vives-project-xp/GreenhouseSecurity/images/affiche-canvas.png

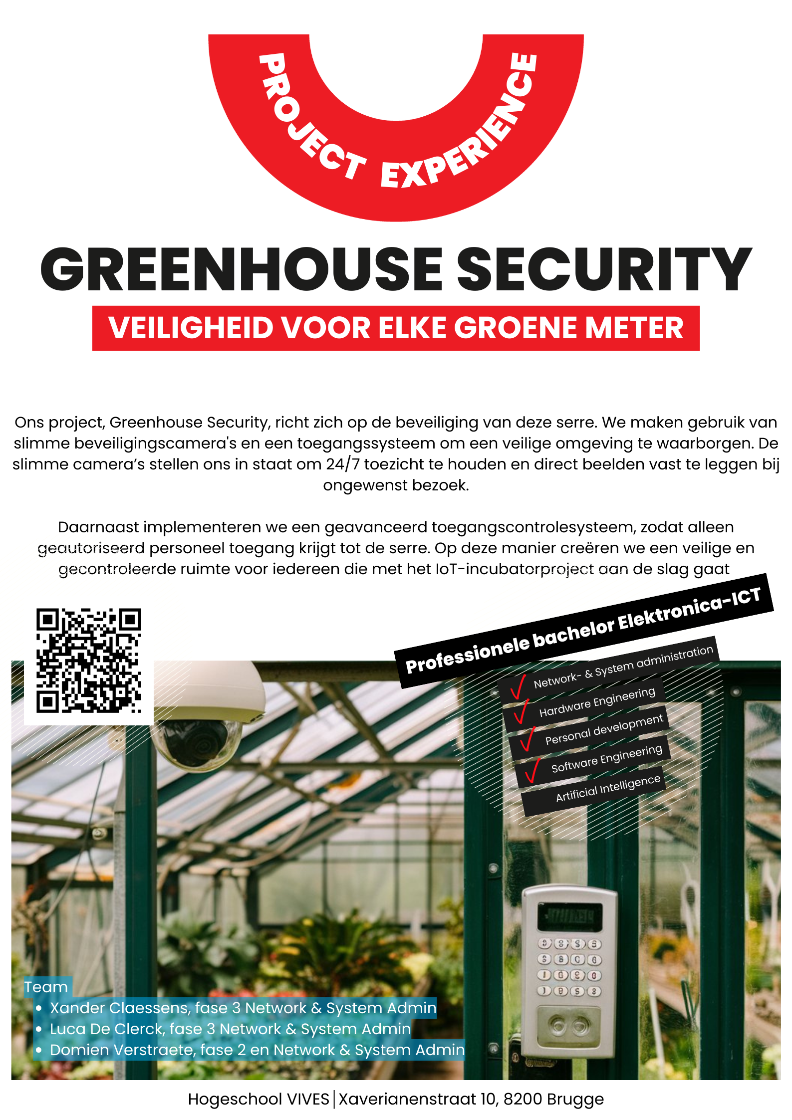
images/affiche-canvas.png
