vives-project-xp/GreenhouseSecurity/images/Architectuur.png

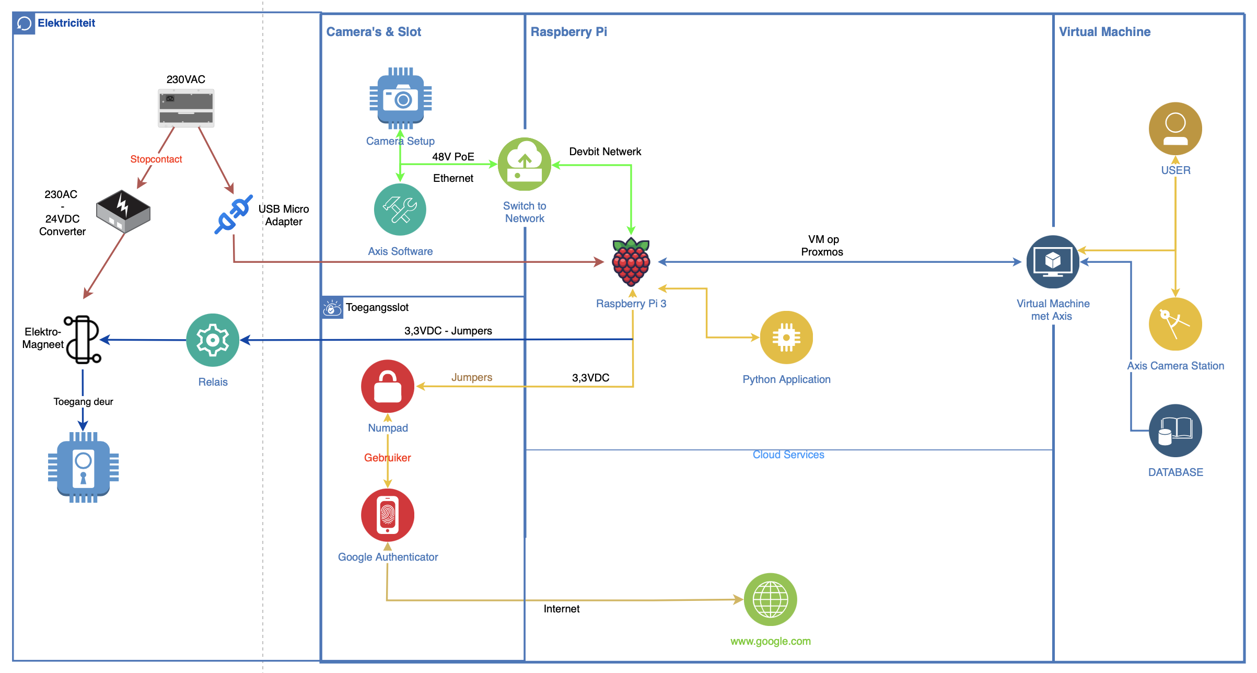
images/Architectuur.png
