vives-project-xp/GreenhouseSecurity/images/axis-application-views.png

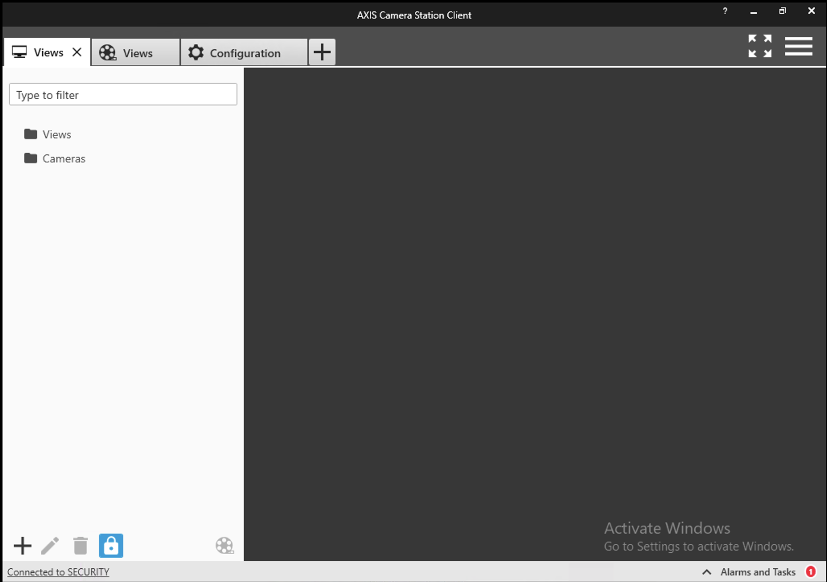
images/axis-application-views.png
