vives-project-xp/GreenhouseSecurity/images/axis.jpg

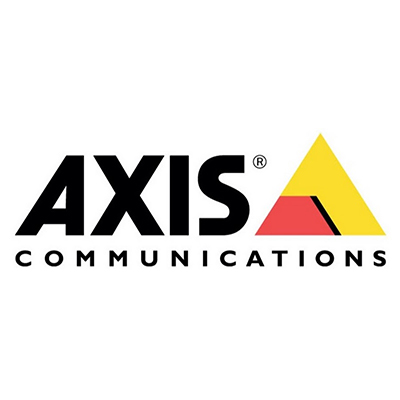
images/axis.jpg
