vives-project-xp/GreenhouseSecurity/images/BiometricImage04192022.jpg

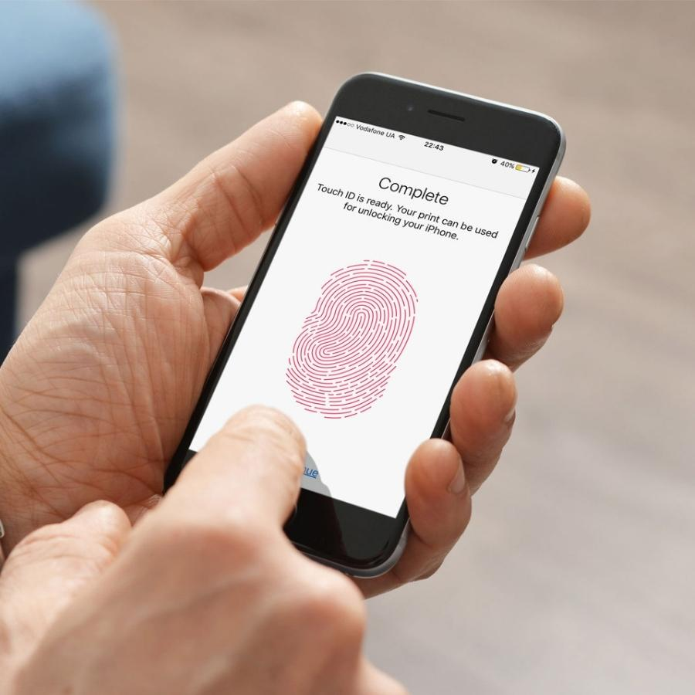
images/BiometricImage04192022.jpg
