vives-project-xp/GreenhouseSecurity/images/camera-dak.jpg

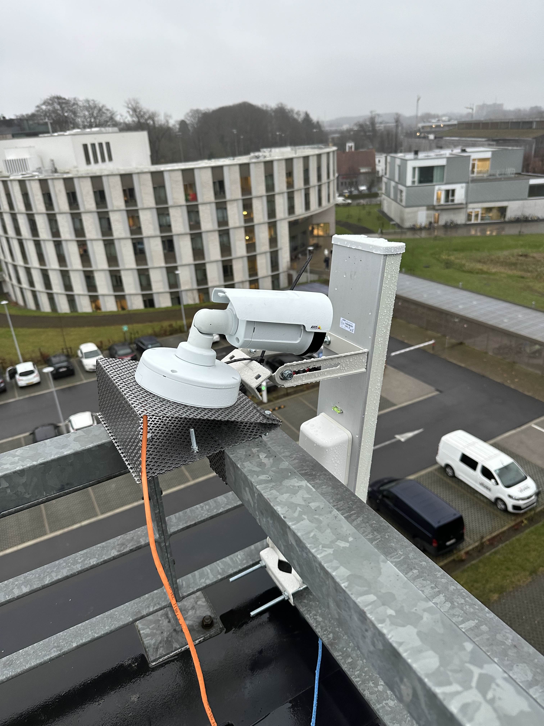
images/camera-dak.jpg
