vives-project-xp/GreenhouseSecurity/images/camera-in-serre.jpg

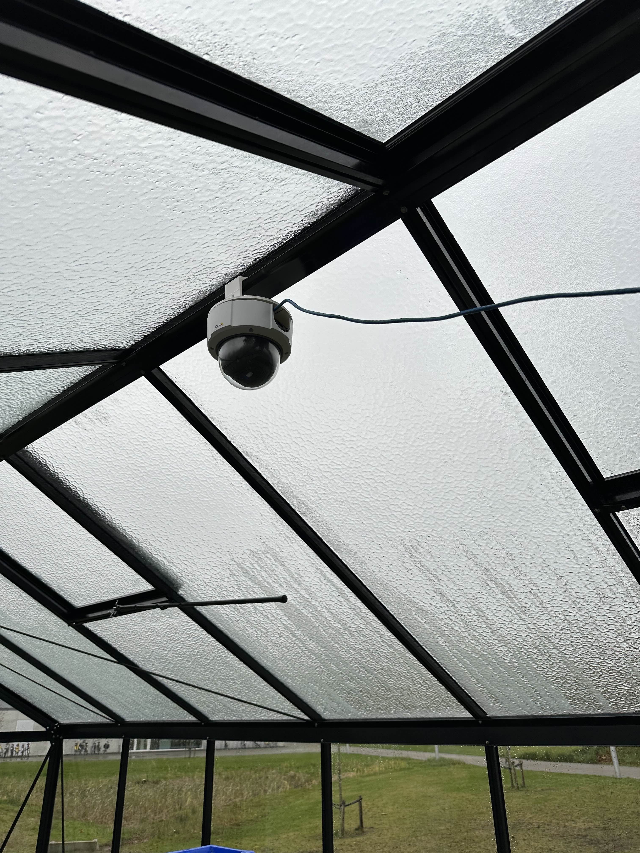
images/camera-in-serre.jpg
