vives-project-xp/GreenhouseSecurity/images/camera-view.png

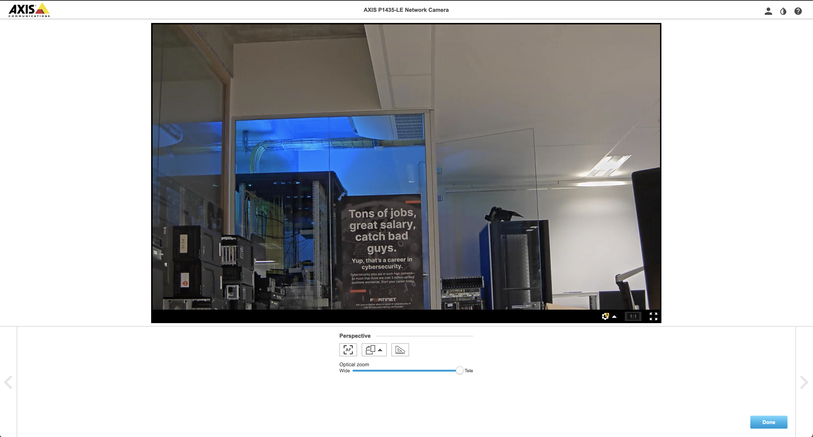
images/camera-view.png
