vives-project-xp/GreenhouseSecurity/images/domeCamera.webp

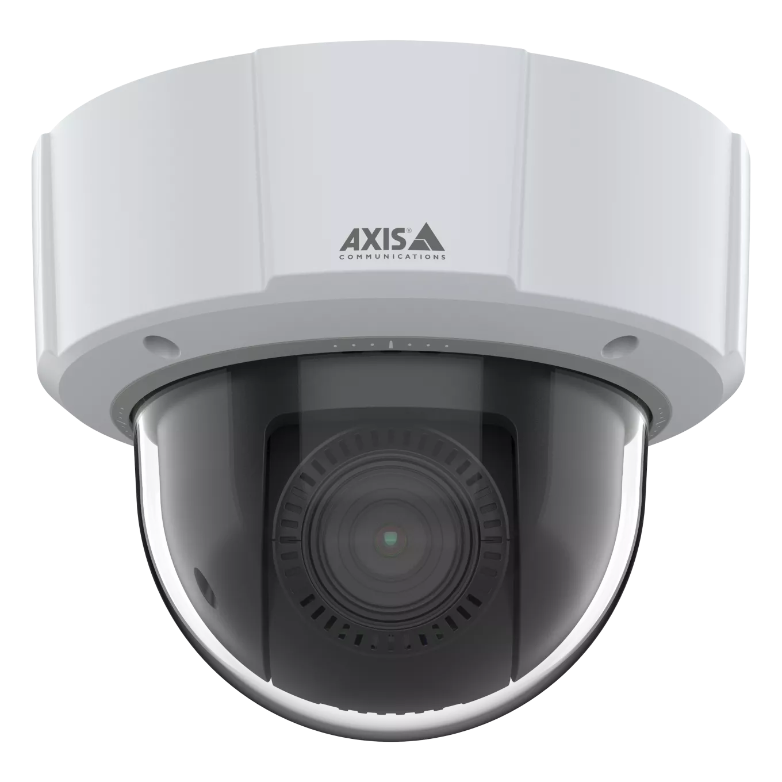
images/domeCamera.webp
