vives-project-xp/GreenhouseSecurity/images/ElektronischSchema.png

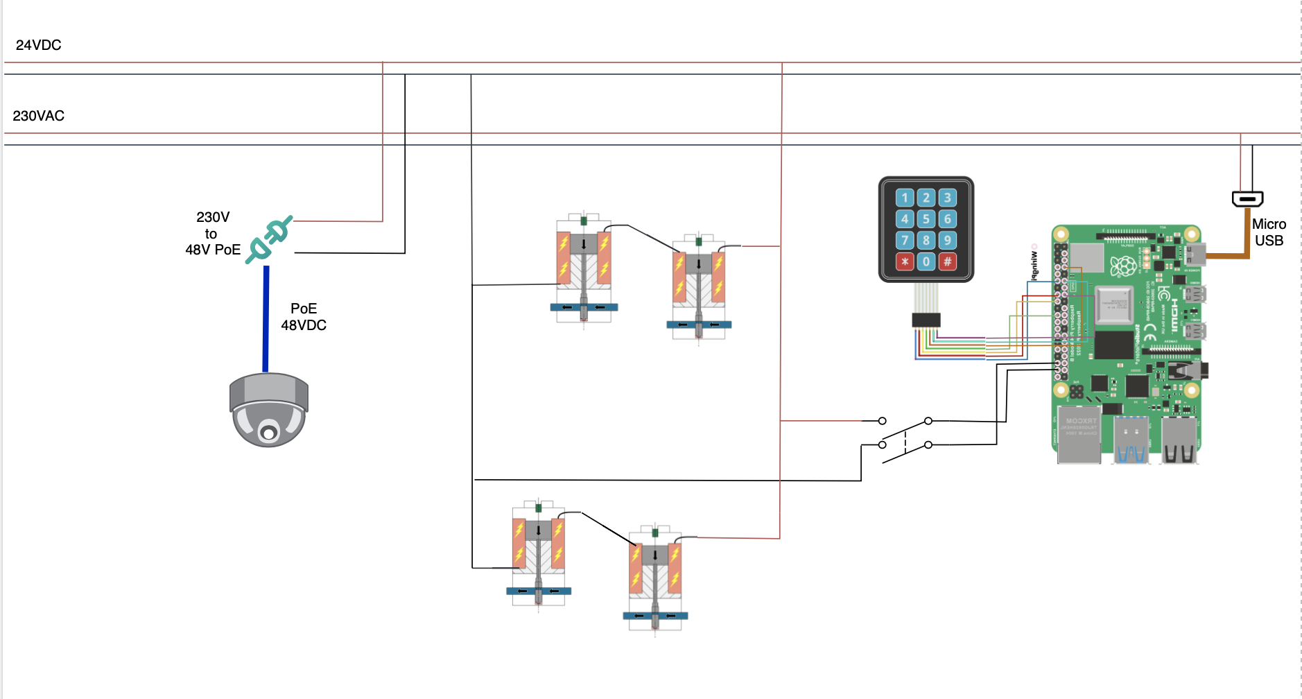
images/ElektronischSchema.png
