vives-project-xp/GreenhouseSecurity/images/google-authenticator.jpg

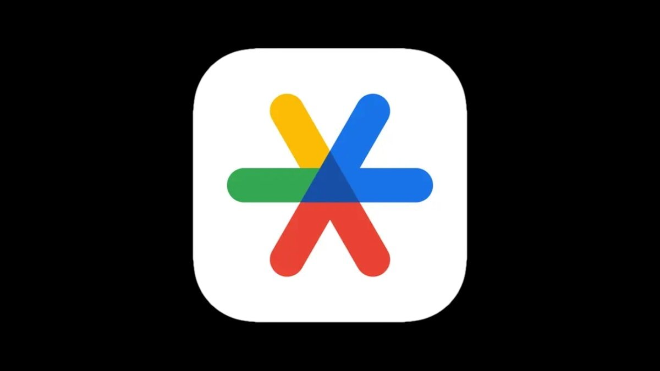
images/google-authenticator.jpg
