vives-project-xp/GreenhouseSecurity/images/google-authenticator.png

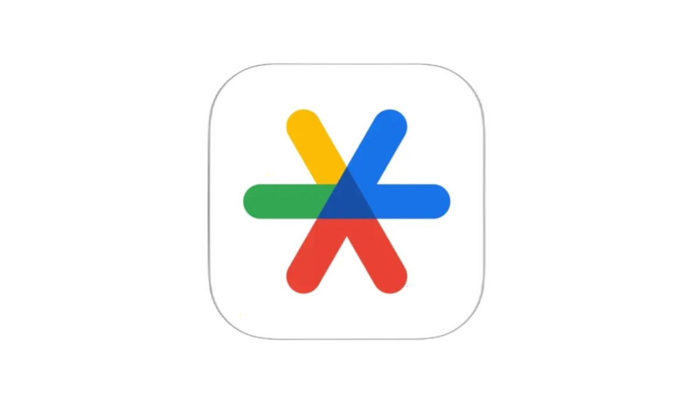
images/google-authenticator.png
