vives-project-xp/GreenhouseSecurity/images/horta-serre.jpg

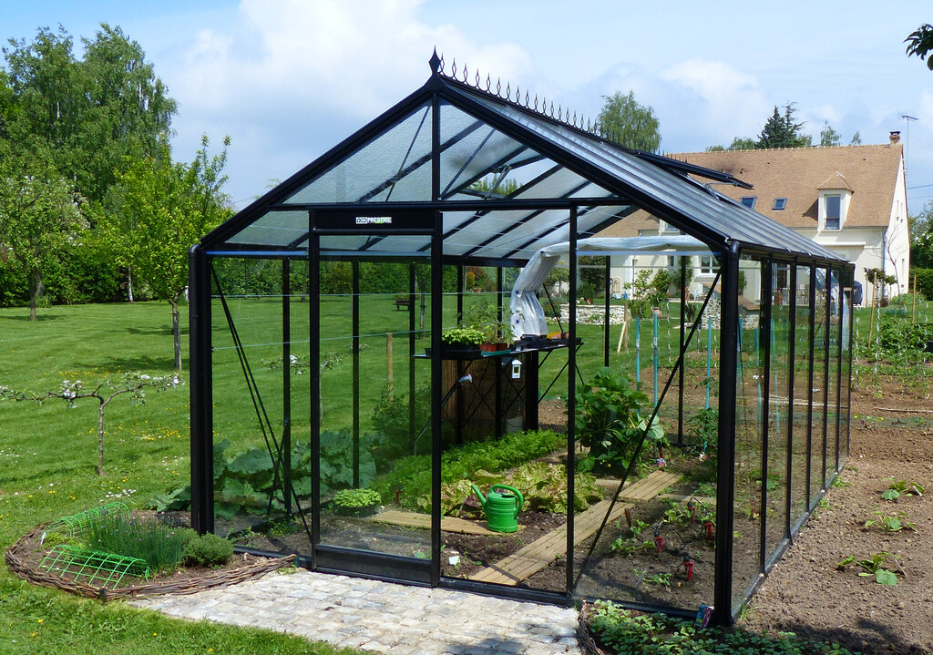
images/horta-serre.jpg
