vives-project-xp/GreenhouseSecurity/images/nfc.jpeg

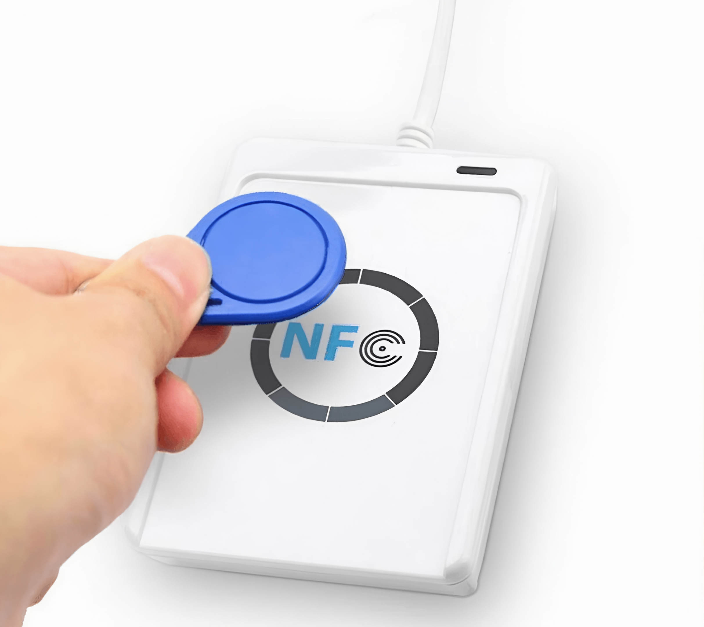
images/nfc.jpeg
