vives-project-xp/GreenhouseSecurity/images/numeriek.jpg

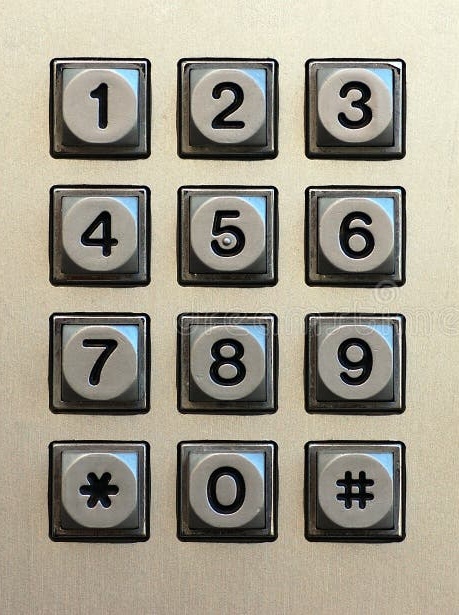
images/numeriek.jpg
