vives-project-xp/GreenhouseSecurity/images/raspbian-desktop.jpg

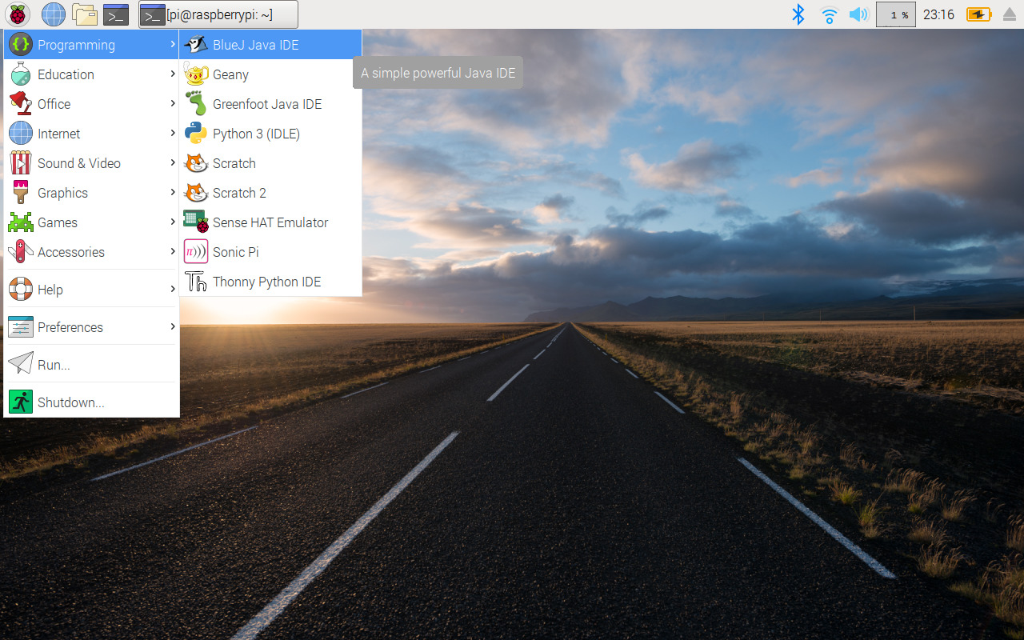
images/raspbian-desktop.jpg
