vives-project-xp/GreenhouseSecurity/images/raspbian.webp

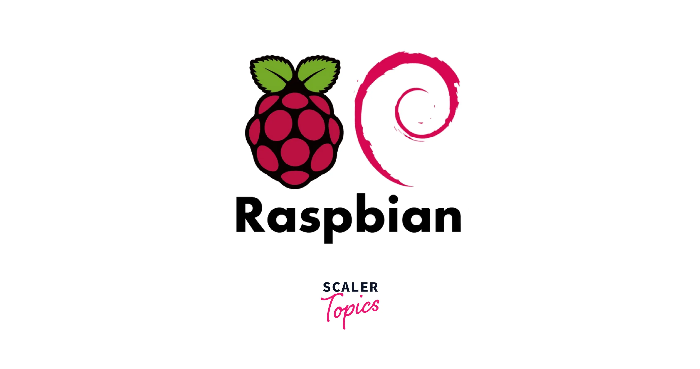
images/raspbian.webp
