vives-project-xp/GreenhouseSecurity/images/schuifdeur.jpg

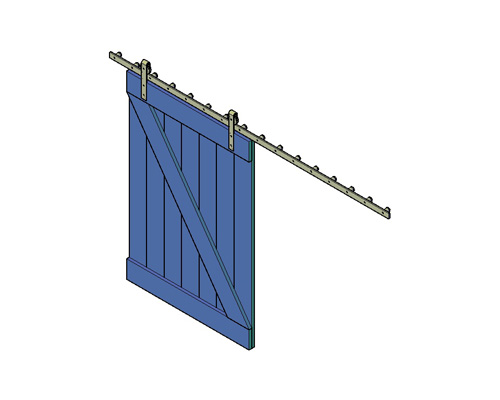
images/schuifdeur.jpg
