vives-project-xp/GreenhouseSecurity/images/voet-front2.0.jpg

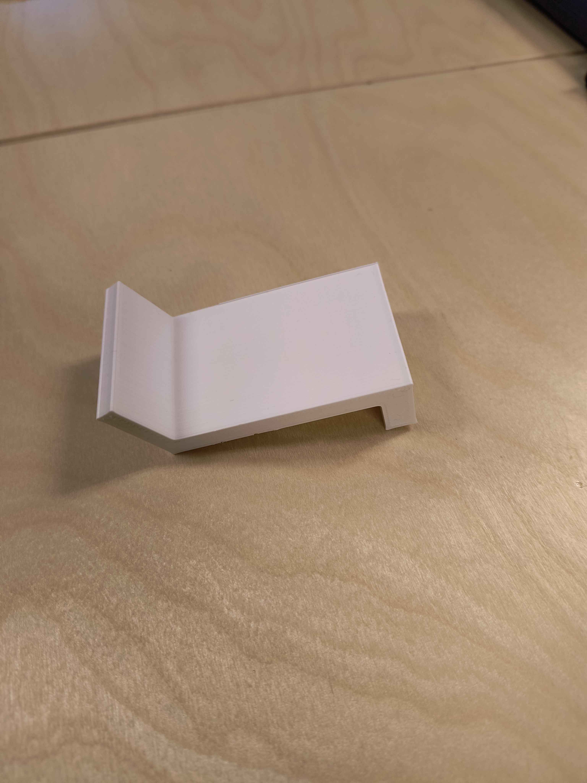
images/voet-front2.0.jpg
