vives-project-xp/GreenhouseSecurity/images/voet-front.jpg

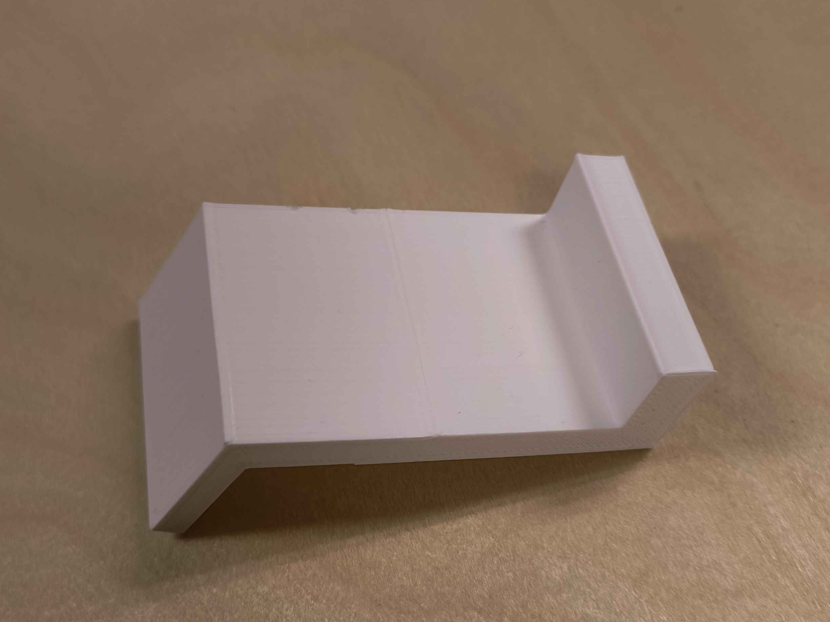
images/voet-front.jpg
