vives-project-xp/GreenhouseSecurity/images/authenticator-steps.jpg

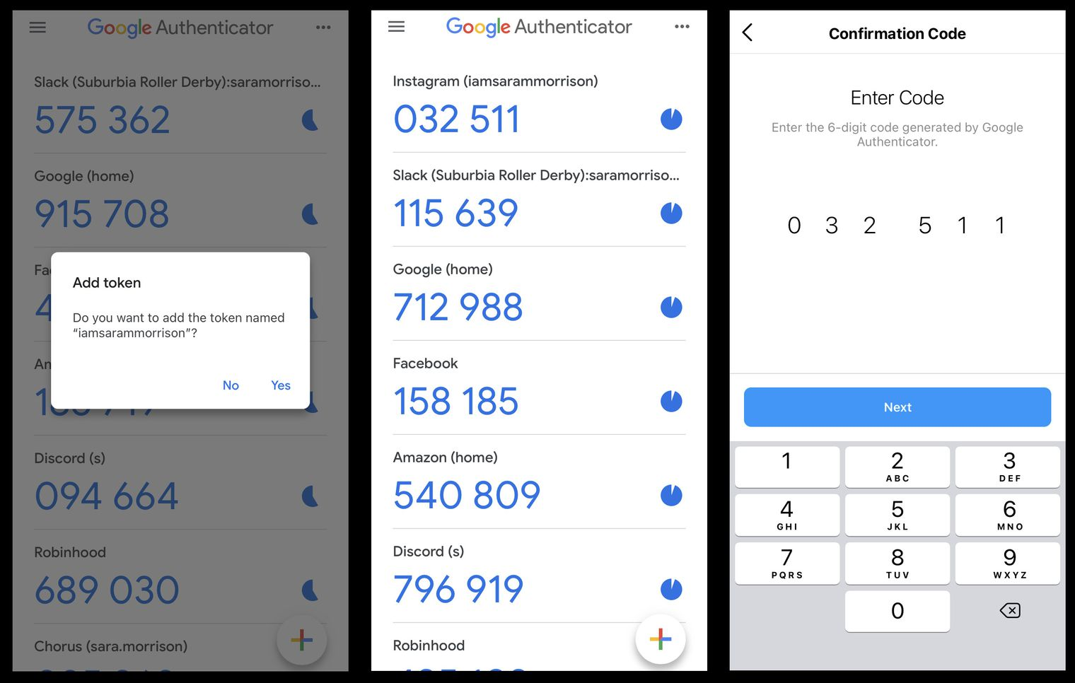
images/authenticator-steps.jpg
